GNUFox/CheapoDemoBoard/pico_adapter/audio.asc

C1: cap; 0.1µ; V=4 Irms=0 Rser=0 Lser=0 mfg="Murata" pn="GRM032R60G104KE15" type="X5R"
C2: cap; 220n
M1: nmos; 2N7002
R1: res; 1k
R2: res; 220
R4: res; 10k
V1: voltage; 3.3
V2: voltage; PULSE(0 3.3 0 1n 1n 1u 5u); AC 3
Named nets: 0, in, out
.tran 0.07
try different values for R3
